jscastonguay/technoshield-ui-hw/hw/lib-kicad/KiCad-Libraries/3D/SourceFiles/SD_Objects/SD-Amp-microSlot-Wings.stl

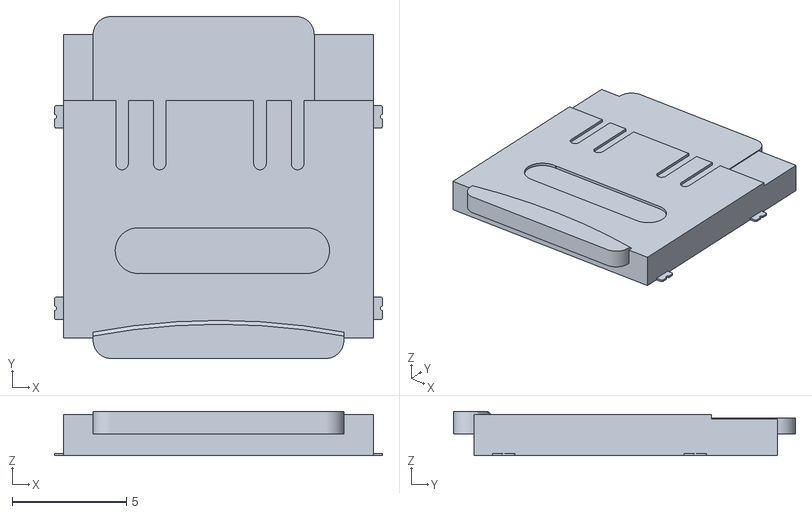
[picture p17: CAD file, 2016-11-25]
hw/lib-kicad/KiCad-Libraries/3D/SourceFiles/SD_Objects/SD-Amp-microSlot-Wings.stl
14.4 x 15.0 x 1.95
