jscastonguay/technoshield-ui-hw/hw/lib-kicad/KiCad-Libraries/3D/SourceFiles/SMD_Passives/SMD-0805-scad.stl

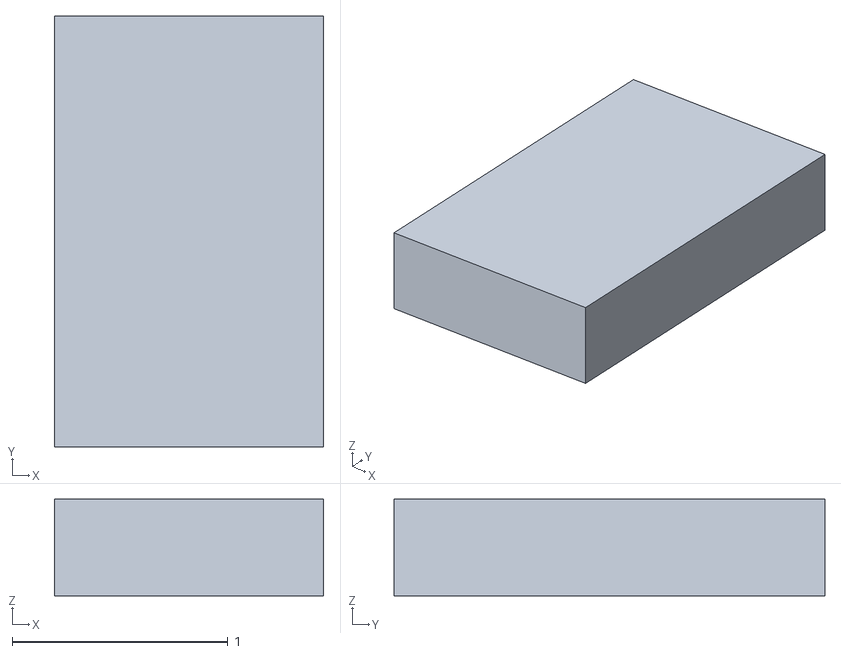
[picture p18: CAD file, 2016-11-25]
hw/lib-kicad/KiCad-Libraries/3D/SourceFiles/SMD_Passives/SMD-0805-scad.stl
1.25 x 2.00 x 0.45
