jscastonguay/technoshield-ui-hw/hw/lib-kicad/KiCad-Libraries/3D/SourceFiles/SOIC/SOIC_08_4.0mm_5.0mm_1.27mm-wings.stl

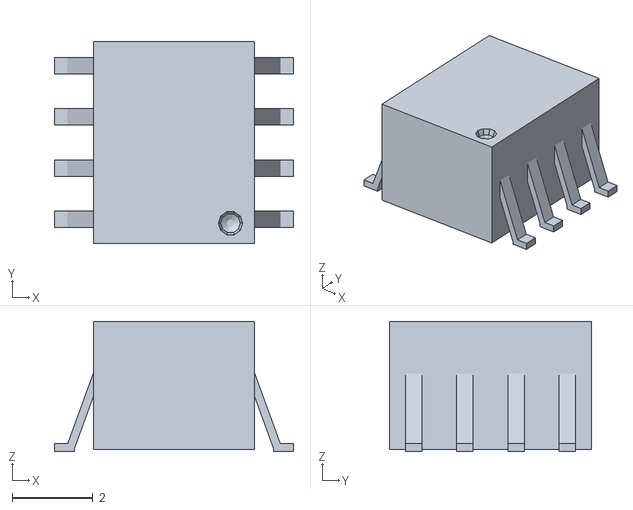
[picture p19: CAD file, 2016-11-25]
hw/lib-kicad/KiCad-Libraries/3D/SourceFiles/SOIC/SOIC_08_4.0mm_5.0mm_1.27mm-wings.stl
5.92 x 5.00 x 3.23
