jscastonguay/technoshield-ui-hw/hw/lib-kicad/KiCad-Libraries/3D/SourceFiles/SolarCells/Spectrolab_TASC1-SCAD.stl

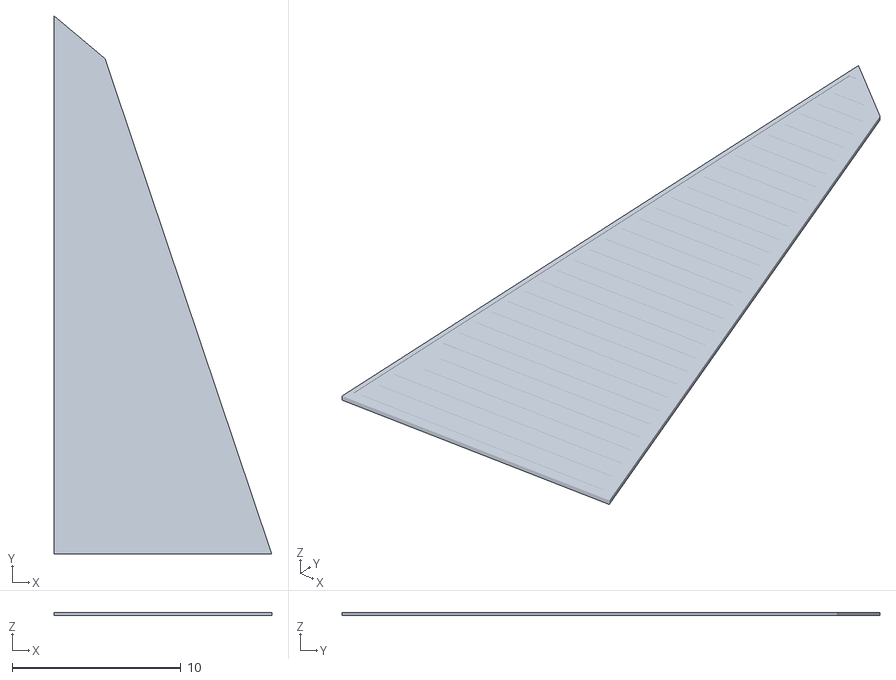
[picture p20: CAD file, 2016-11-25]
hw/lib-kicad/KiCad-Libraries/3D/SourceFiles/SolarCells/Spectrolab_TASC1-SCAD.stl
12.9 x 31.9 x 0.178
