jscastonguay/technoshield-ui-hw/hw/lib-kicad/KiCad-Libraries/3D/SourceFiles/SON-10/SON-10-scad.stl

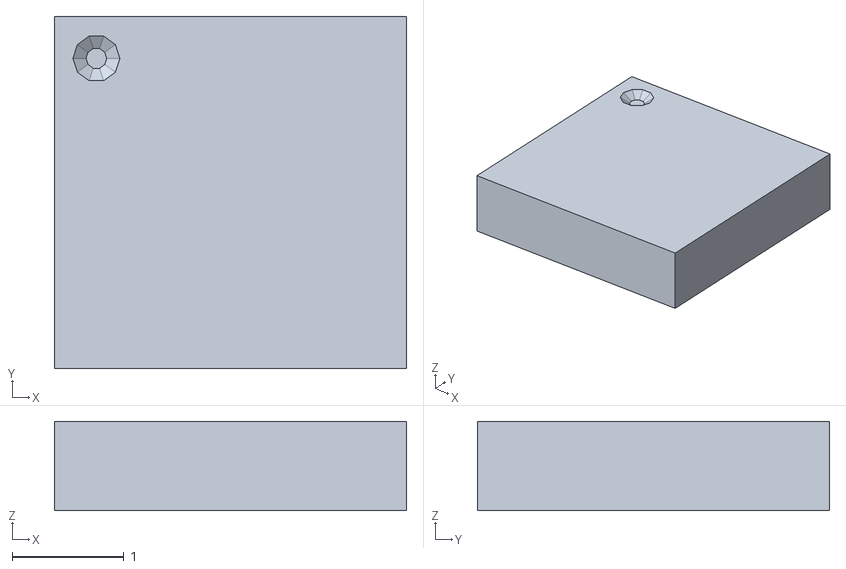
[picture p21: CAD file, 2016-11-25]
hw/lib-kicad/KiCad-Libraries/3D/SourceFiles/SON-10/SON-10-scad.stl
3.15 x 3.15 x 0.8
