jscastonguay/technoshield-ui-hw/hw/lib-kicad/KiCad-Libraries/3D/SourceFiles/SOT-23/SOT-23-6-wings.stl

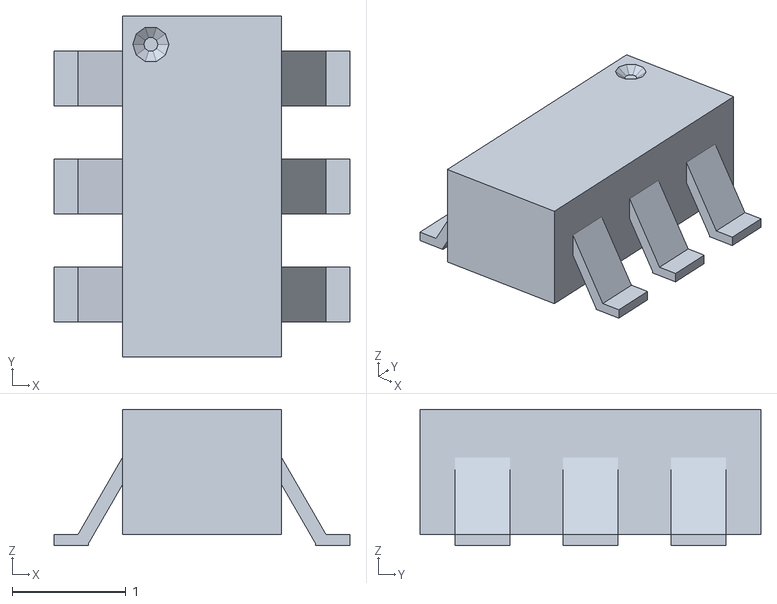
[picture p22: CAD file, 2016-11-25]
hw/lib-kicad/KiCad-Libraries/3D/SourceFiles/SOT-23/SOT-23-6-wings.stl
2.60 x 3.00 x 1.20
