jscastonguay/technoshield-ui-hw/hw/lib-kicad/KiCad-Libraries/3D/SourceFiles/SOT-363/SOT-363-SCAD.stl

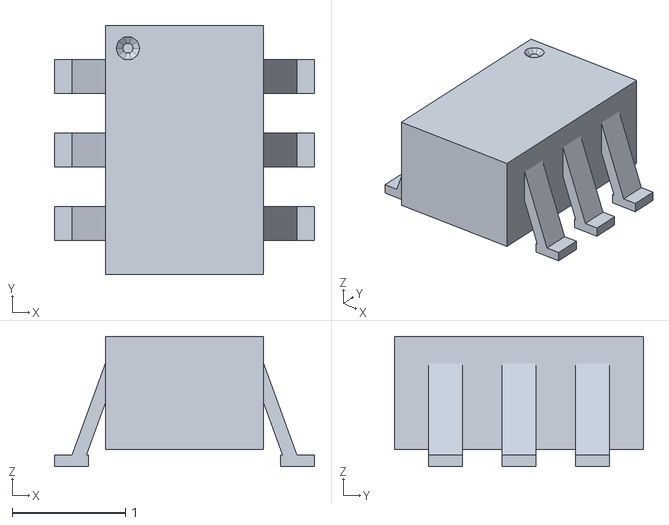
[picture p23: CAD file, 2016-11-25]
hw/lib-kicad/KiCad-Libraries/3D/SourceFiles/SOT-363/SOT-363-SCAD.stl
2.30 x 2.20 x 1.15
