jscastonguay/technoshield-ui-hw/hw/lib-kicad/KiCad-Libraries/3D/SourceFiles/SSOP/SSOP_20_4.5mm_6.6mm_0.65mm-wings.stl

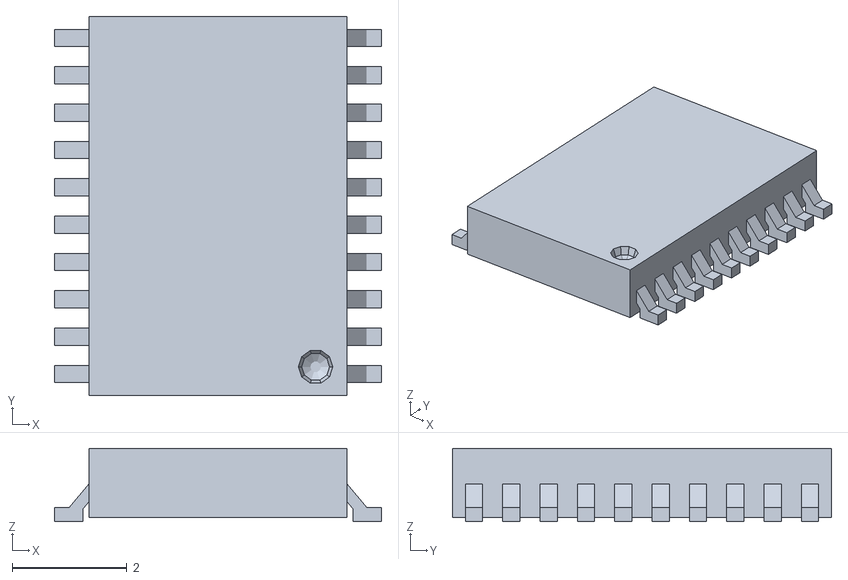
[picture p24: CAD file, 2016-11-25]
hw/lib-kicad/KiCad-Libraries/3D/SourceFiles/SSOP/SSOP_20_4.5mm_6.6mm_0.65mm-wings.stl
5.70 x 6.60 x 1.28
