jscastonguay/technoshield-ui-hw/hw/lib-kicad/KiCad-Libraries/3D/SourceFiles/Switches/Switch-DIP-SMD-3-Wings.stl

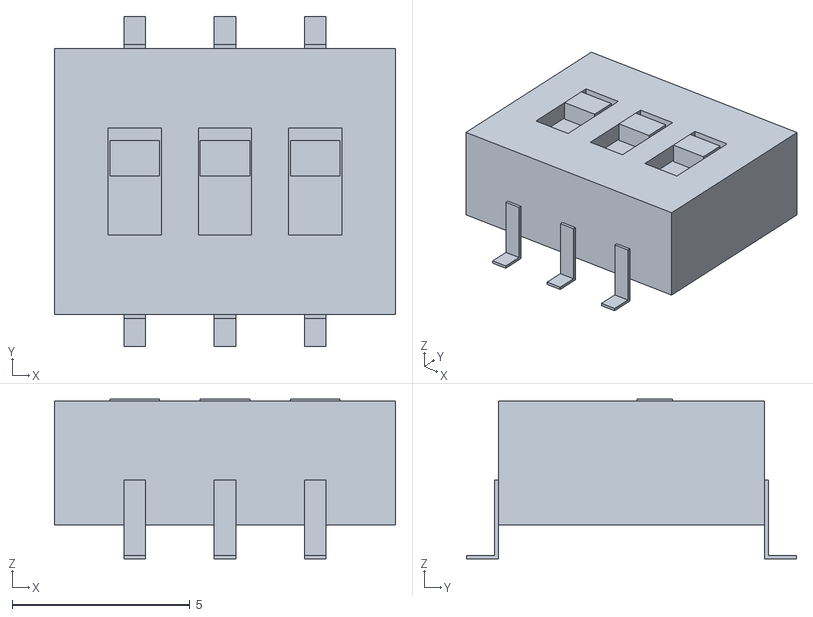
[picture p25: CAD file, 2016-11-25]
hw/lib-kicad/KiCad-Libraries/3D/SourceFiles/Switches/Switch-DIP-SMD-3-Wings.stl
9.60 x 9.30 x 4.50
