jscastonguay/technoshield-ui-hw/hw/lib-kicad/KiCad-Libraries/3D/SourceFiles/Venus638/Venus638-Wings.stl

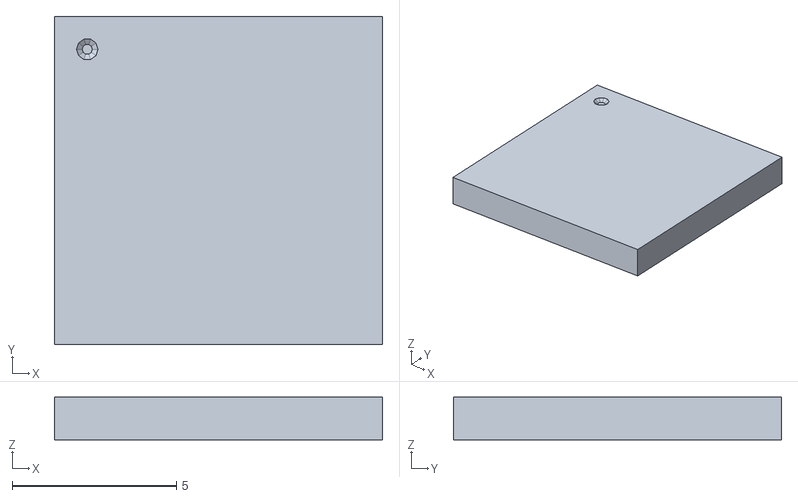
[picture p26: CAD file, 2016-11-25]
hw/lib-kicad/KiCad-Libraries/3D/SourceFiles/Venus638/Venus638-Wings.stl
10.0 x 10.0 x 1.30
