jscastonguay/technoshield-ui-hw/hw/lib-kicad/KiCad-Libraries/3D/SourceFiles/Connectors/CONN_1x6/CONN_1x6_Male.stl

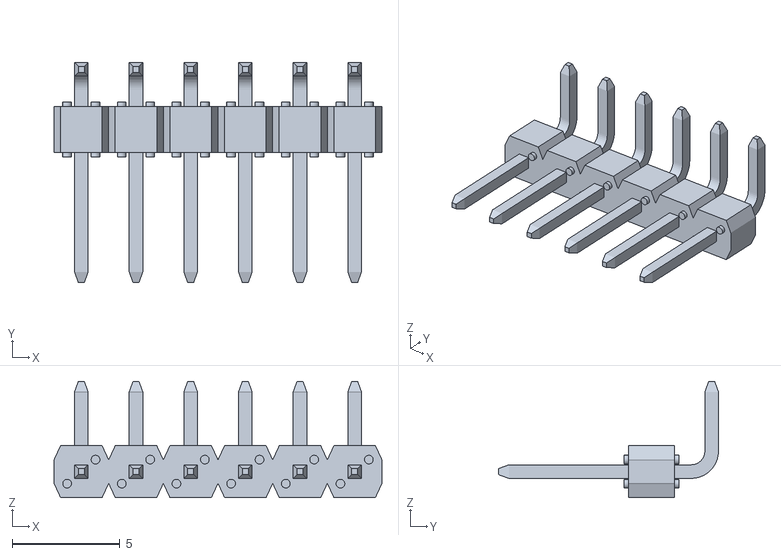
[picture p27: CAD file, 2016-11-25]
hw/lib-kicad/KiCad-Libraries/3D/SourceFiles/Connectors/CONN_1x6/CONN_1x6_Male.stl
15.2 x 10.2 x 5.40
