jscastonguay/technoshield-ui-hw/hw/lib-kicad/KiCad-Libraries/3D/SourceFiles/Connectors/CONN_2x6/CONN_2x6_Female.stl

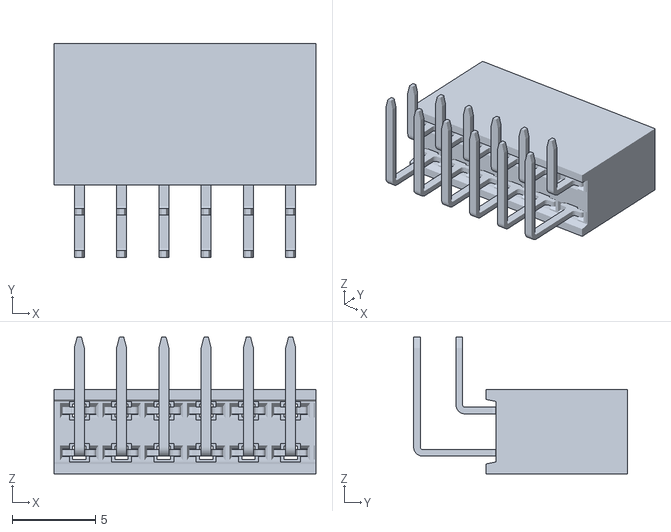
[picture p28: CAD file, 2016-11-25]
hw/lib-kicad/KiCad-Libraries/3D/SourceFiles/Connectors/CONN_2x6/CONN_2x6_Female.stl
15.7 x 12.8 x 8.23
