jscastonguay/technoshield-ui-hw/hw/lib-kicad/KiCad-Libraries/3D/SourceFiles/Connectors/Deans/Deans-SCAD.stl

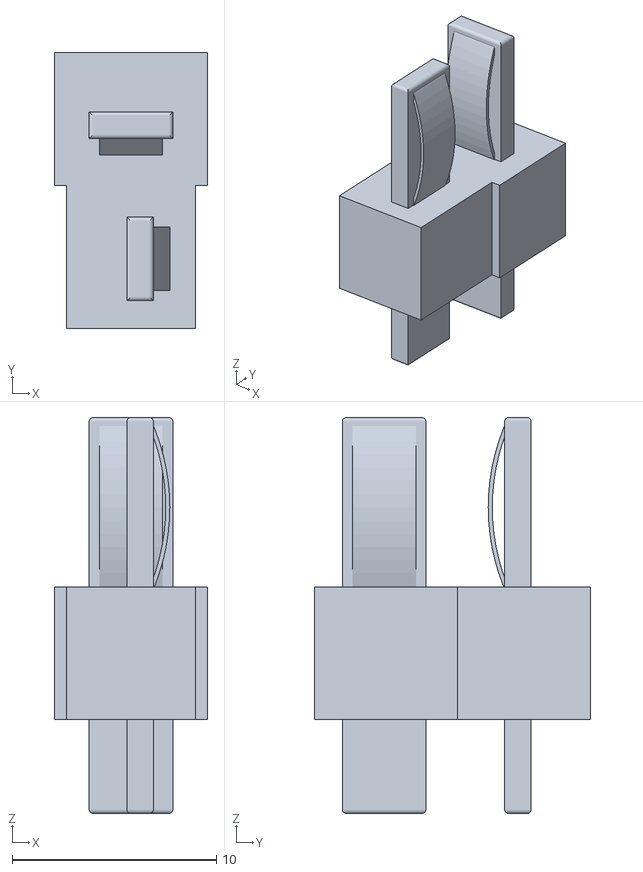
[picture p29: CAD file, 2016-11-25]
hw/lib-kicad/KiCad-Libraries/3D/SourceFiles/Connectors/Deans/Deans-SCAD.stl
7.50 x 13.5 x 19.4
