jscastonguay/technoshield-ui-hw/hw/lib-kicad/KiCad-Libraries/3D/SourceFiles/SD_Objects/SD-Amp-microSlot-SCAD.stl

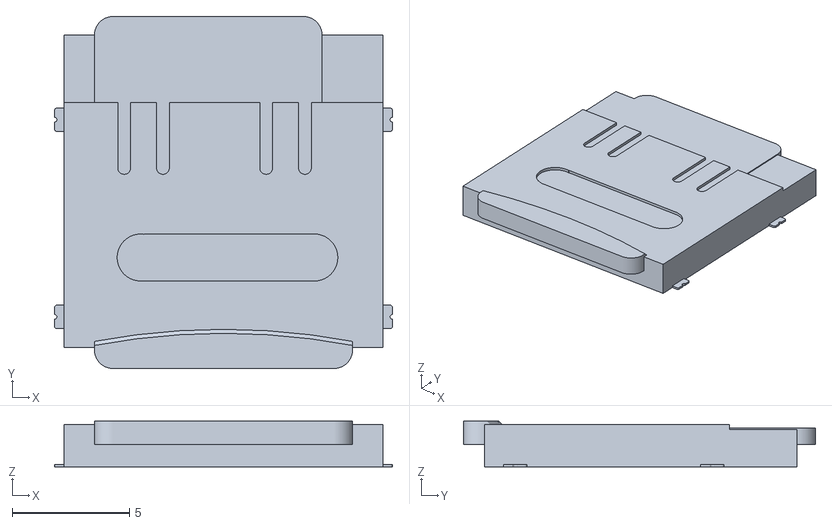
[picture p30: CAD file, 2016-11-25]
hw/lib-kicad/KiCad-Libraries/3D/SourceFiles/SD_Objects/SD-Amp-microSlot-SCAD.stl
14.4 x 15.0 x 1.95
