jscastonguay/technoshield-ui-hw/hw/lib-kicad/KiCad-Libraries/3D/SourceFiles/SolarCells/Spectrolab_CIC-SCAD.stl

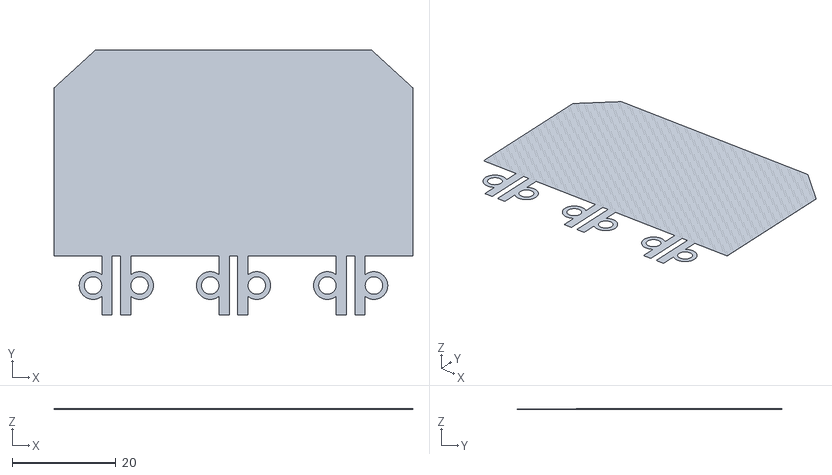
[picture p31: CAD file, 2016-11-25]
hw/lib-kicad/KiCad-Libraries/3D/SourceFiles/SolarCells/Spectrolab_CIC-SCAD.stl
69.1 x 51.1 x 0.178
