jscastonguay/technoshield-ui-hw/hw/lib-kicad/KiCad-Libraries/3D/SourceFiles/SON-10/SON-10-wings.stl

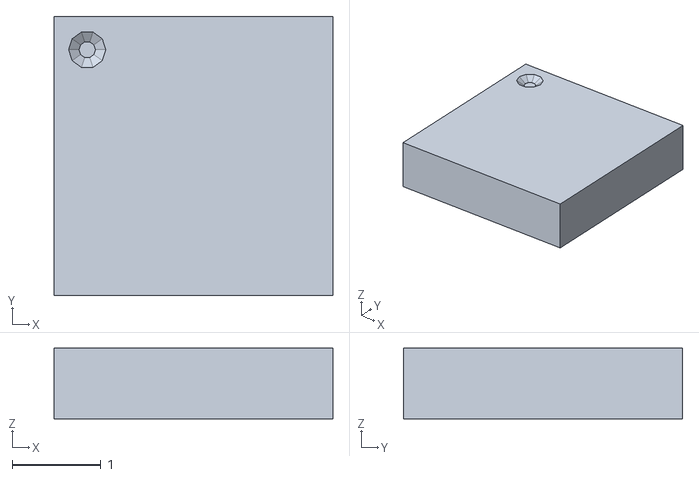
[picture p32: CAD file, 2016-11-25]
hw/lib-kicad/KiCad-Libraries/3D/SourceFiles/SON-10/SON-10-wings.stl
3.15 x 3.15 x 0.8
