jscastonguay/technoshield-ui-hw/hw/lib-kicad/KiCad-Libraries/3D/SourceFiles/SSOP/SSOP_08_3.0mm_3.0mm_0.65mm-scad.stl

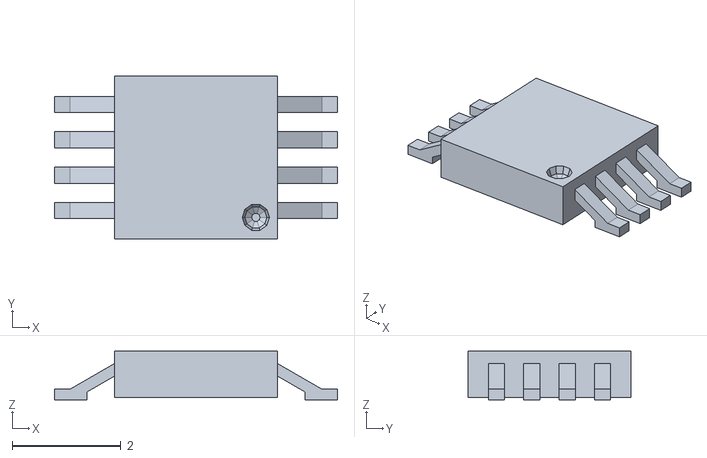
[picture p33: CAD file, 2016-11-25]
hw/lib-kicad/KiCad-Libraries/3D/SourceFiles/SSOP/SSOP_08_3.0mm_3.0mm_0.65mm-scad.stl
5.20 x 3.00 x 0.9
