jscastonguay/technoshield-ui-hw/hw/lib-kicad/KiCad-Libraries/3D/SourceFiles/Switches/Switch-Eswitch-Slide-SCAD.stl

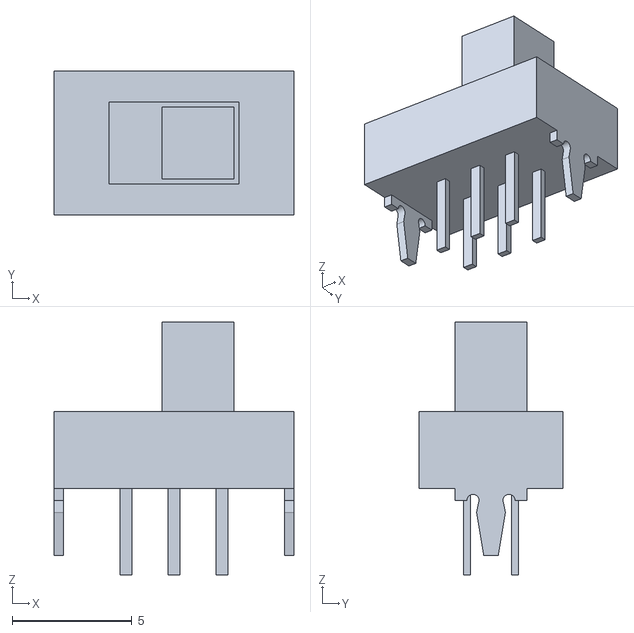
[picture p34: CAD file, 2016-11-25]
hw/lib-kicad/KiCad-Libraries/3D/SourceFiles/Switches/Switch-Eswitch-Slide-SCAD.stl
10.0 x 6.00 x 10.5
