jscastonguay/technoshield-ui-hw/hw/lib-kicad/KiCad-Libraries/3D/SourceFiles/SMD_Passives/SMD-1206-scad.stl

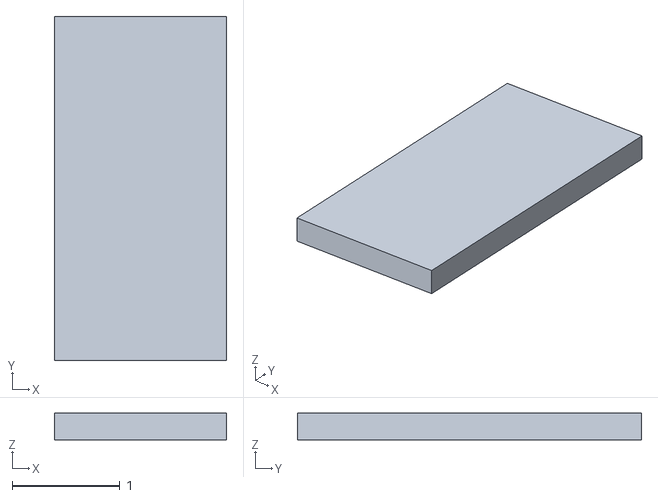
[picture p35: CAD file, 2016-11-25]
hw/lib-kicad/KiCad-Libraries/3D/SourceFiles/SMD_Passives/SMD-1206-scad.stl
1.60 x 3.20 x 0.25
