jscastonguay/technoshield-ui-hw/hw/lib-kicad/KiCad-Libraries/3D/SourceFiles/SOIC/SOIC_08_4.0mm_5.8mm_1.27mm-scad.stl

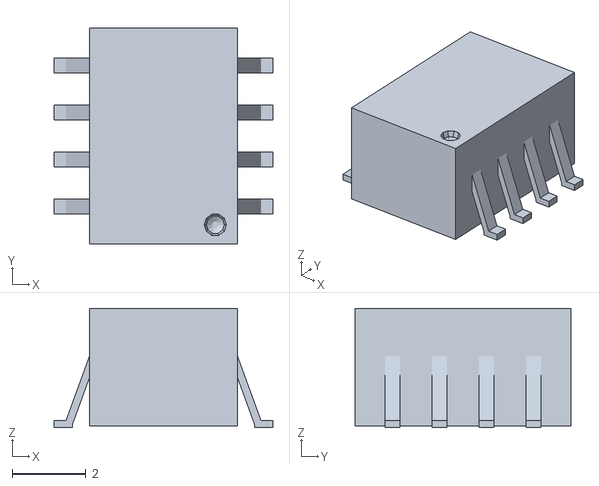
[picture p36: CAD file, 2016-11-25]
hw/lib-kicad/KiCad-Libraries/3D/SourceFiles/SOIC/SOIC_08_4.0mm_5.8mm_1.27mm-scad.stl
5.92 x 5.84 x 3.23
