jscastonguay/technoshield-ui-hw/hw/lib-kicad/KiCad-Libraries/3D/SourceFiles/Switches/Switch-TE-Slide-Wings.stl

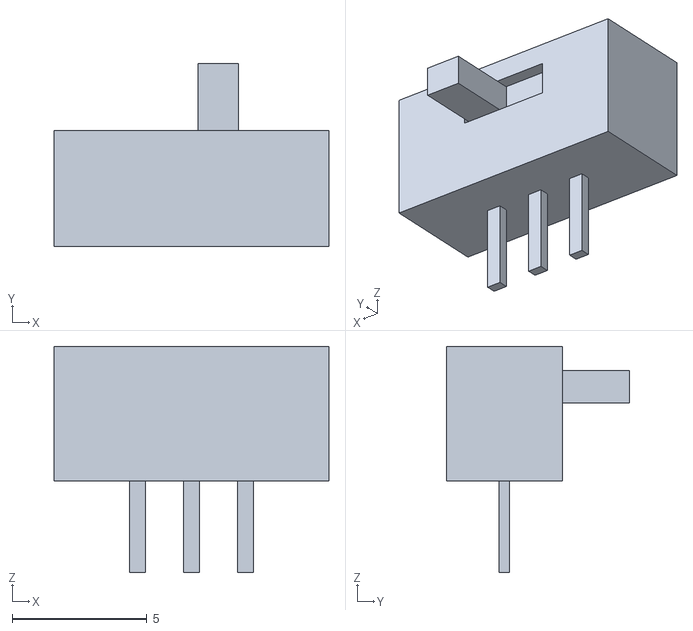
[picture p37: CAD file, 2016-11-25]
hw/lib-kicad/KiCad-Libraries/3D/SourceFiles/Switches/Switch-TE-Slide-Wings.stl
10.2 x 6.80 x 8.40
