jscastonguay/technoshield-ui-hw/hw/lib-kicad/KiCad-Libraries/3D/SourceFiles/SMD_Passives/SMD-2010-scad.stl

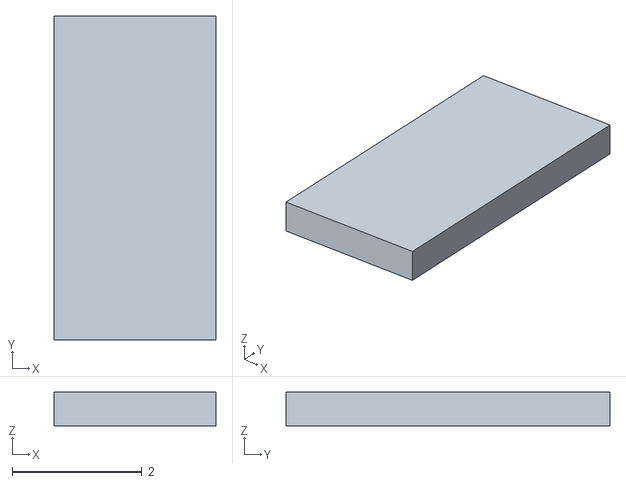
[picture p38: CAD file, 2016-11-25]
hw/lib-kicad/KiCad-Libraries/3D/SourceFiles/SMD_Passives/SMD-2010-scad.stl
2.50 x 5.00 x 0.52
